ccadic/esp32reflow/Untitled.JPG

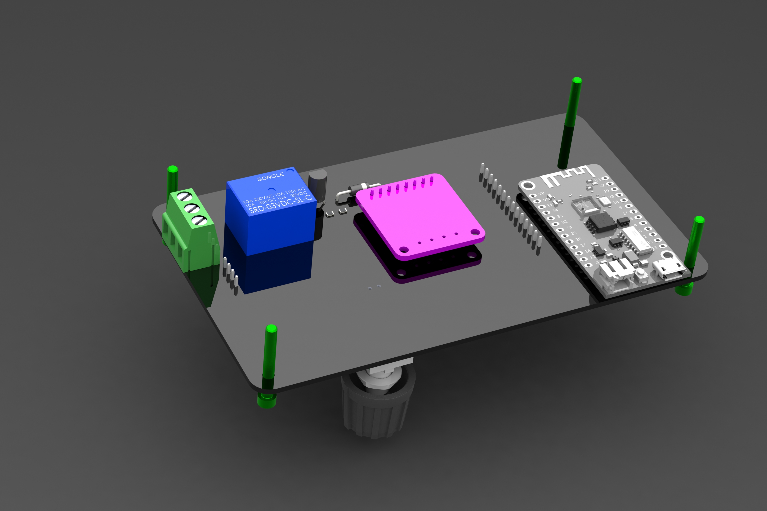
Untitled.JPG
